ldab/WimB/pics/battery_25.png

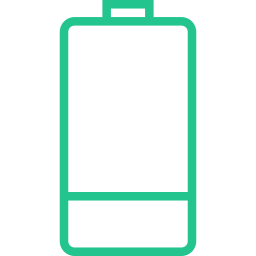
pics/battery_25.png
